LU6APR/ESP32_C3_MINI_MORSE_TRAINER/IMG_0012.jpg

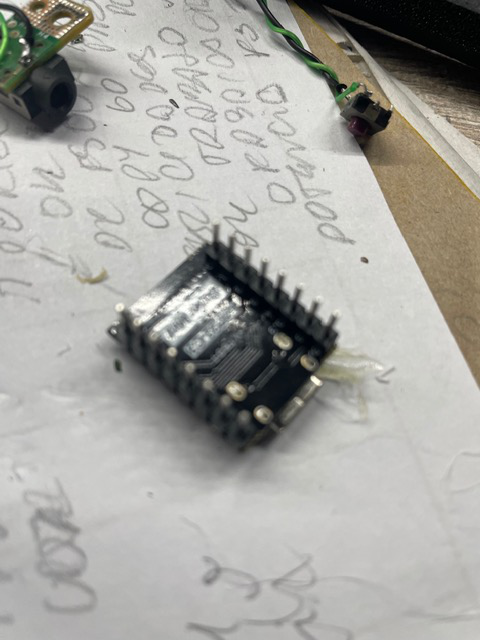
IMG_0012.jpg
