LU6APR/ESP32_C3_MINI_MORSE_TRAINER/WhatsApp Image 2026-05-29 at 12.50.39.jpeg

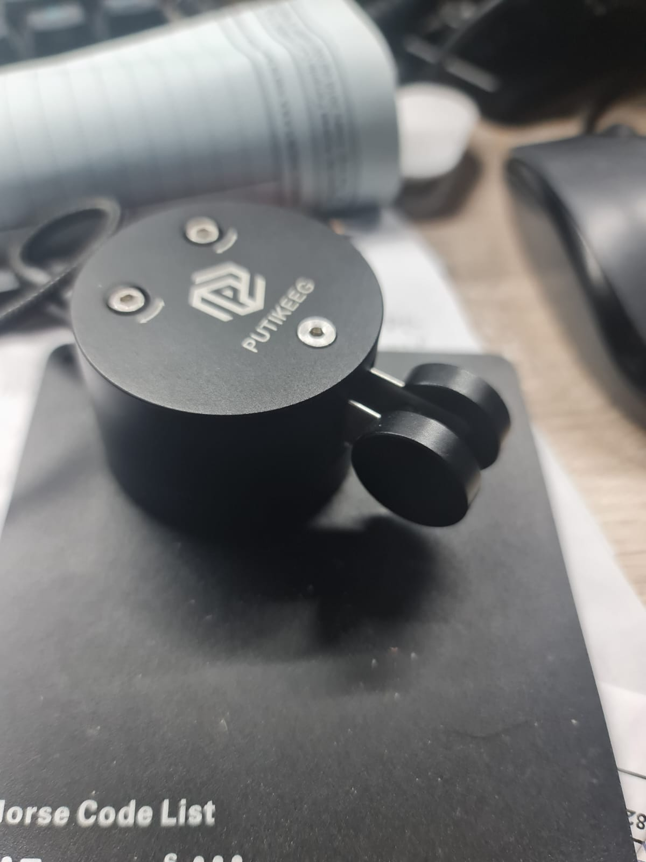
WhatsApp Image 2026-05-29 at 12.50.39.jpeg
